Gwardii/Swarm-of-Mobile-Robots/Camera/images/1.jpg

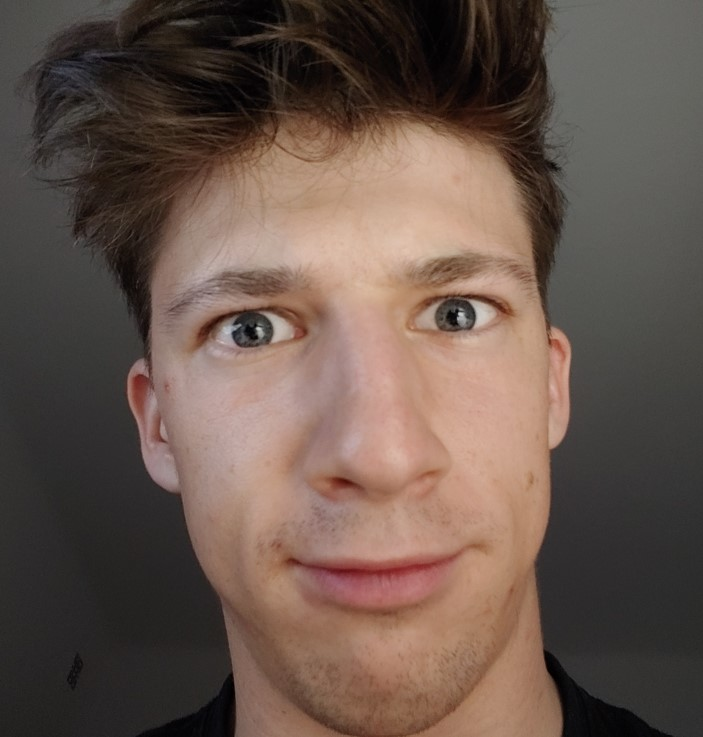
Camera/images/1.jpg
