Gwardii/Swarm-of-Mobile-Robots/Camera/images/2.jpg

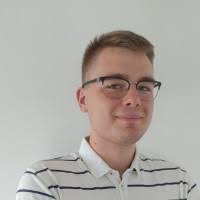
Camera/images/2.jpg
