Gwardii/Swarm-of-Mobile-Robots/Camera/images/3.jpg

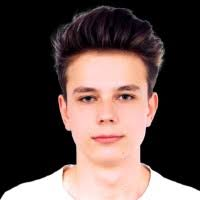
Camera/images/3.jpg
