Gwardii/Swarm-of-Mobile-Robots/Camera/images/7.jpg

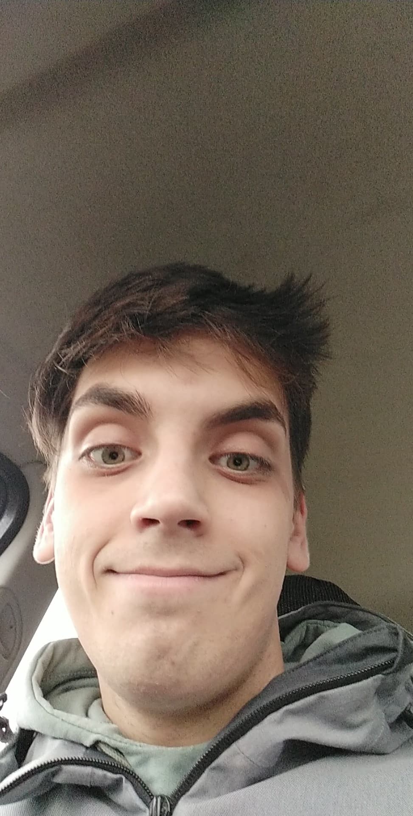
Camera/images/7.jpg
