Gwardii/Swarm-of-Mobile-Robots/Camera/images/9.jpg

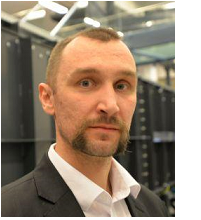
Camera/images/9.jpg
