Gwardii/Swarm-of-Mobile-Robots/Camera/images/10.jpg

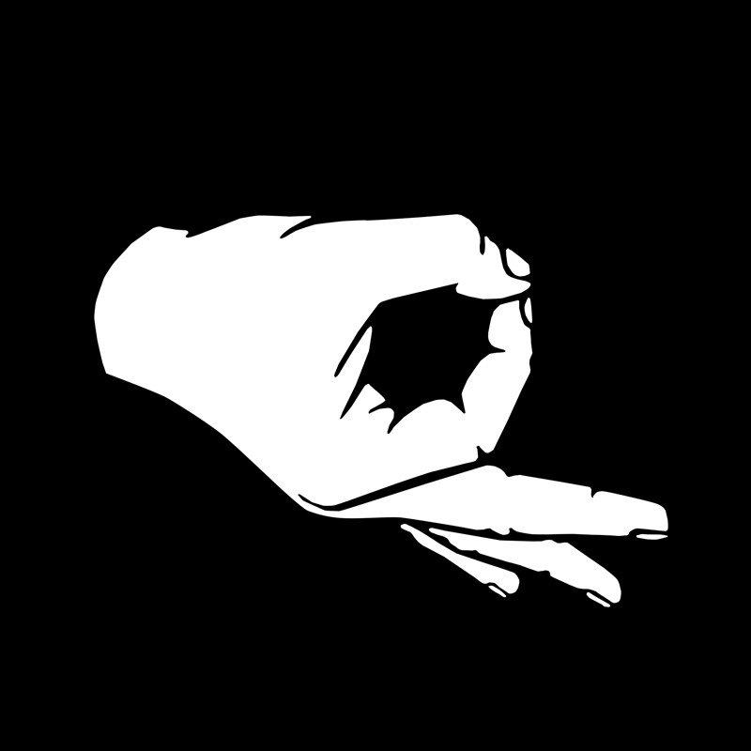
Camera/images/10.jpg
