Gwardii/Swarm-of-Mobile-Robots/Camera/images/11.jpg

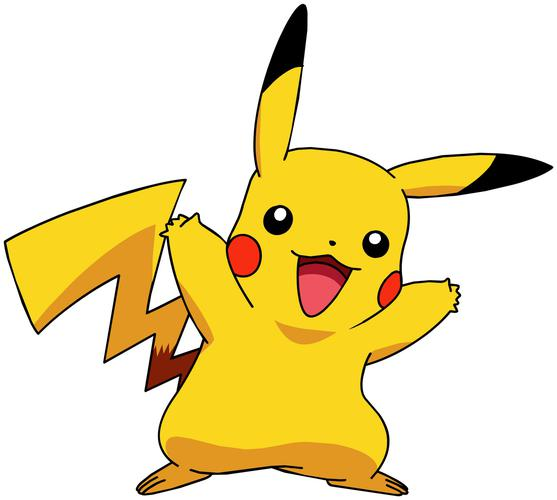
Camera/images/11.jpg
