Gwardii/Swarm-of-Mobile-Robots/Camera/images/12.jpg

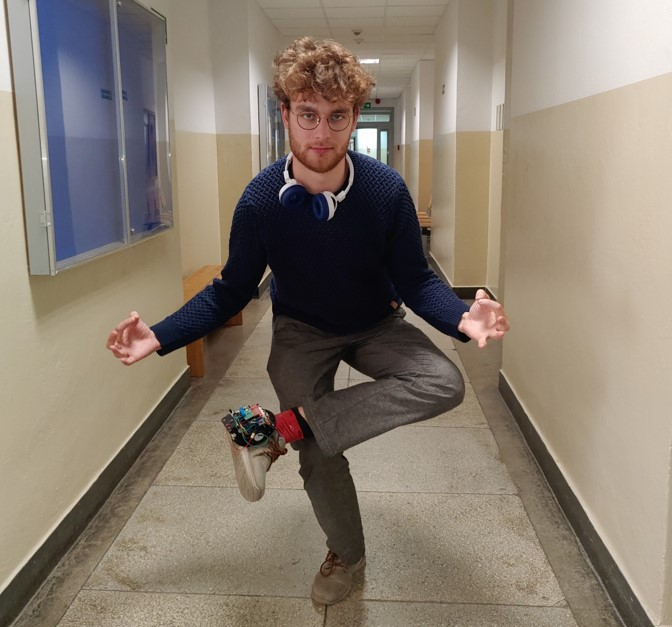
Camera/images/12.jpg
