Gwardii/Swarm-of-Mobile-Robots/Camera/images/13.jpg

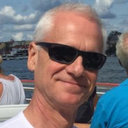
Camera/images/13.jpg
