Gwardii/Swarm-of-Mobile-Robots/Camera/images/14.jpg

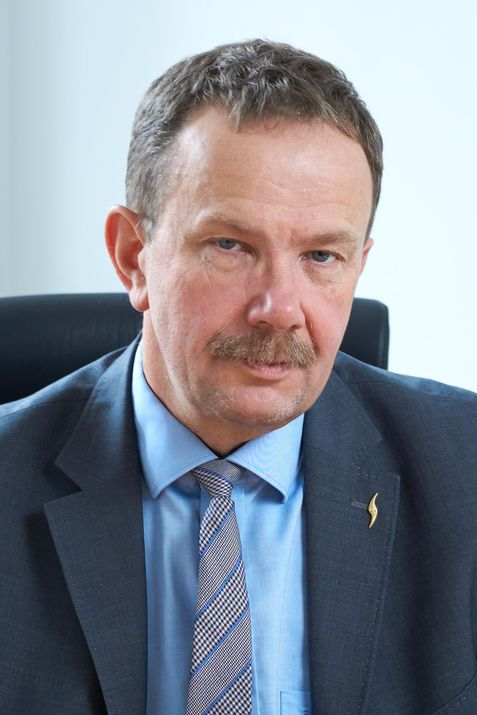
Camera/images/14.jpg
