Gwardii/Swarm-of-Mobile-Robots/Camera/images/17.jpg

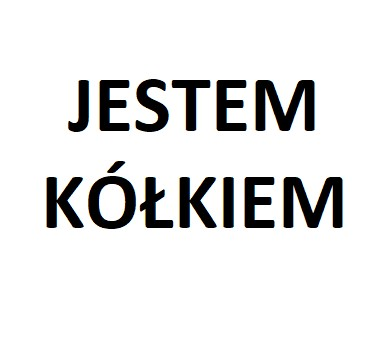
Camera/images/17.jpg
