Gwardii/Swarm-of-Mobile-Robots/Camera/images/18.jpg

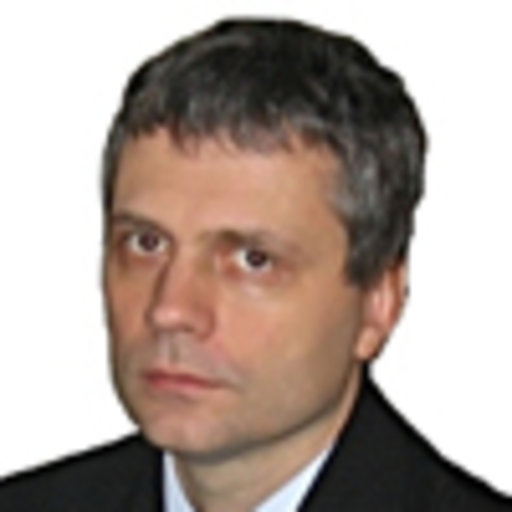
Camera/images/18.jpg
