Gwardii/Swarm-of-Mobile-Robots/Computer/modele/budowanie mapy.drawio.png

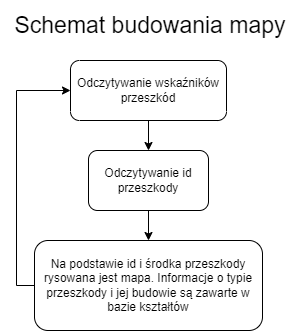
Computer/modele/budowanie mapy.drawio.png
