Gwardii/Swarm-of-Mobile-Robots/Readme_img/GUI.png

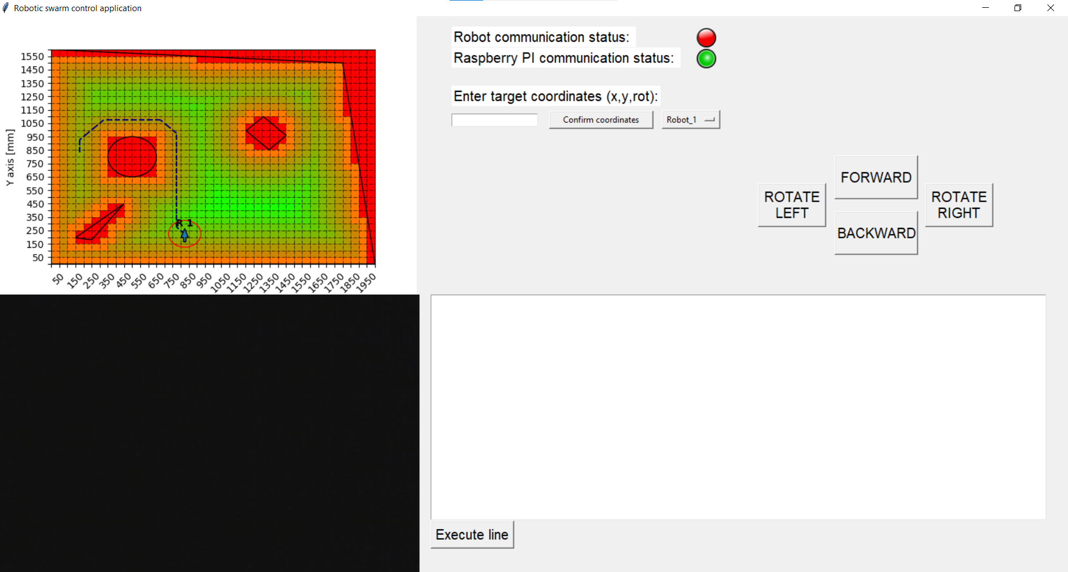
Readme_img/GUI.png
