Gwardii/Swarm-of-Mobile-Robots/Camera/captured_frames/calibration_img_1.png

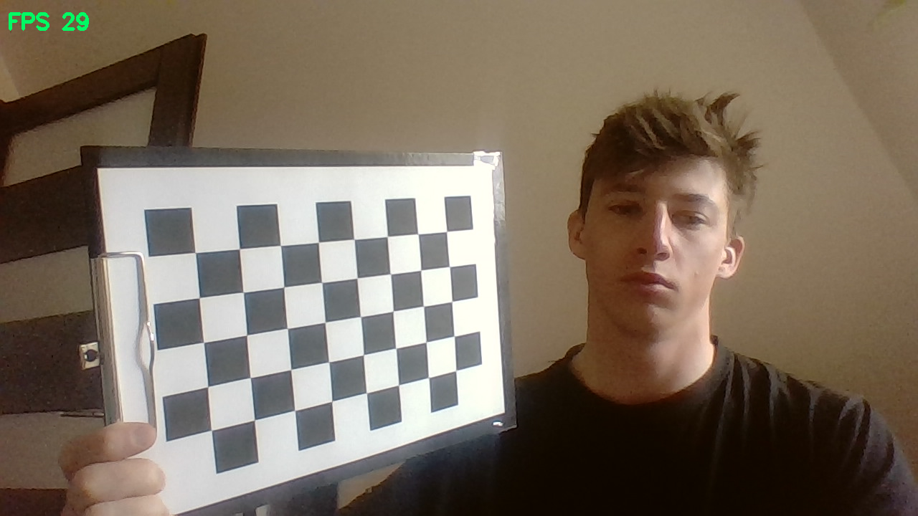
Camera/captured_frames/calibration_img_1.png
