Gwardii/Swarm-of-Mobile-Robots/Camera/captured_frames/calibration_img_2.png

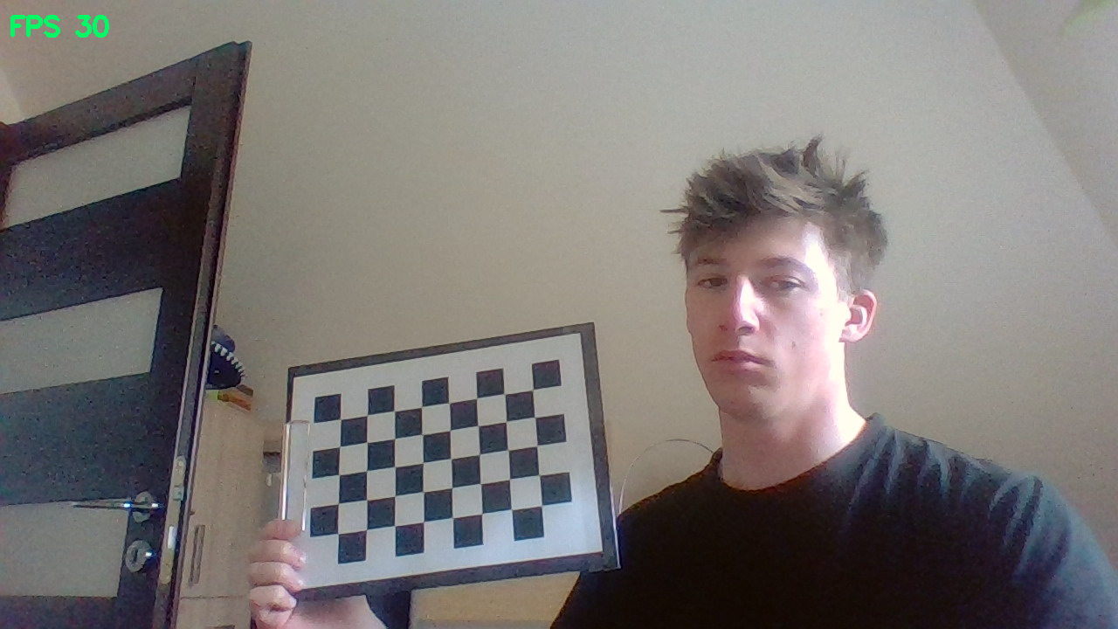
Camera/captured_frames/calibration_img_2.png
