Gwardii/Swarm-of-Mobile-Robots/Camera/captured_frames/calibration_img_3.png

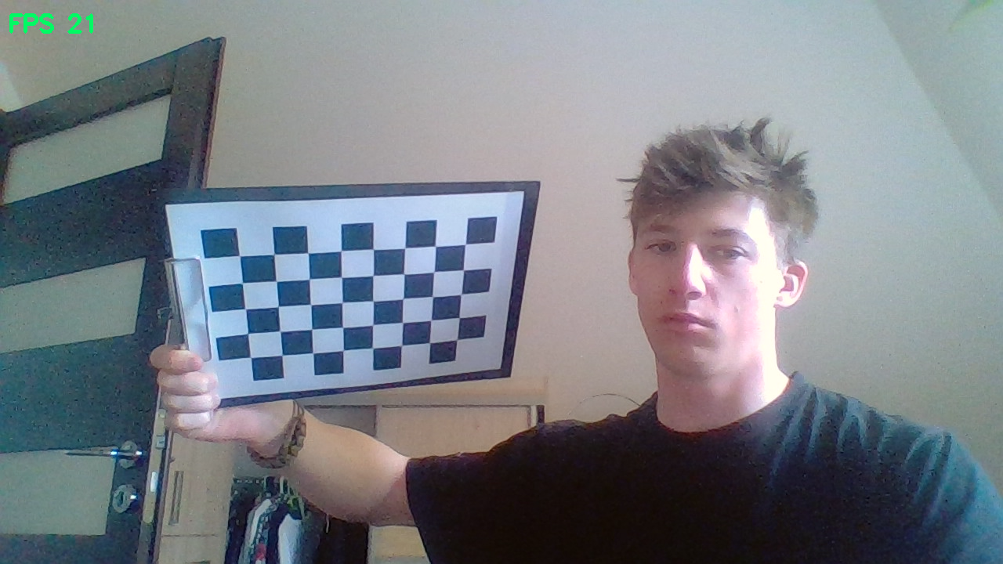
Camera/captured_frames/calibration_img_3.png
