Gwardii/Swarm-of-Mobile-Robots/Camera/captured_frames/calibration_img_8.png

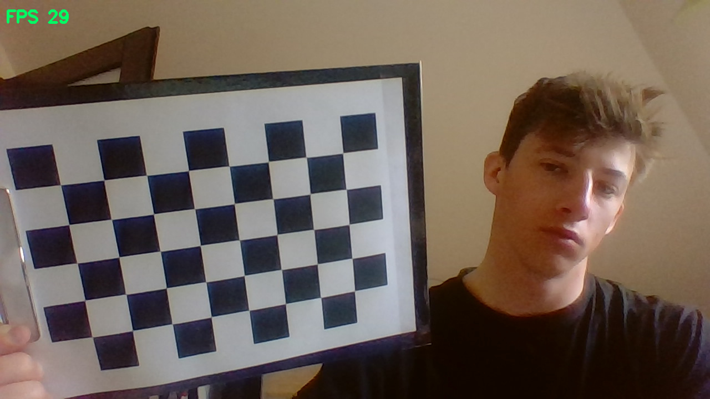
Camera/captured_frames/calibration_img_8.png
