Gwardii/Swarm-of-Mobile-Robots/Camera/captured_frames/calibration_img_9.png

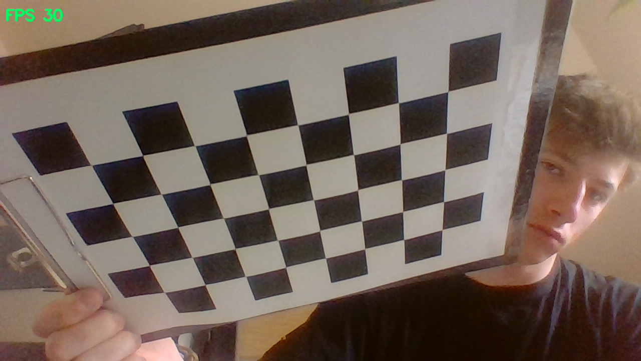
Camera/captured_frames/calibration_img_9.png
